ihartwig/amtdoor3/pcb/wobbuffet-bg.png

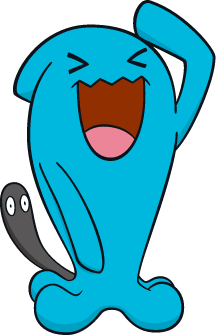
pcb/wobbuffet-bg.png
